tommy-gilligan/rp235x-nokia-3310/rp/src/backlight.rs

use embassy_rp::{
    gpio::{Level, Output},
    peripherals::PIN_15,
};
use shared::Backlight;

pub struct Light<'a>(Output<'a>);

impl Light<'_> {
    pub fn new(pin: PIN_15) -> Self {
        Self(Output::new(pin, Level::Low))
    }
}

impl Backlight for Light<'_> {
    fn on(&mut self) {
        self.0.set_high();
    }

    fn off(&mut self) {
        self.0.set_low();
    }
}
