tommy-gilligan/rp235x-nokia-3310/web/src/display.rs

use embedded_graphics::{
    Pixel,
    pixelcolor::BinaryColor,
    prelude::{Dimensions, DrawTarget},
    primitives::Rectangle,
};
use embedded_graphics_web_simulator::{
    display::WebSimulatorDisplay, output_settings::OutputSettingsBuilder,
};
use web_sys::Element;

pub struct Display(WebSimulatorDisplay<embedded_graphics::pixelcolor::BinaryColor>);

impl Display {
    pub fn new(element: Element) -> Self {
        let output_settings = OutputSettingsBuilder::new()
            .scale(1)
            .pixel_spacing(0)
            .alpha_color(embedded_graphics::pixelcolor::BinaryColor::On)
            .build();

        let display: WebSimulatorDisplay<embedded_graphics::pixelcolor::BinaryColor> =
            WebSimulatorDisplay::new((84, 48), &output_settings, Some(&element));

        Self(display)
    }
}

impl DrawTarget for Display {
    type Color = BinaryColor;

    type Error = <WebSimulatorDisplay<BinaryColor> as DrawTarget>::Error;

    fn draw_iter<I: IntoIterator<Item = Pixel<<Self as DrawTarget>::Color>>>(
        &mut self,
        i: I,
    ) -> Result<(), <Self as DrawTarget>::Error> {
        let a = self.0.draw_iter(i);
        let _ = self.0.flush();
        a
    }
}

impl Dimensions for Display {
    fn bounding_box(&self) -> Rectangle {
        self.0.bounding_box()
    }
}
